jamozu/multisensor/pics/Pic_AQS_Base02.jpg

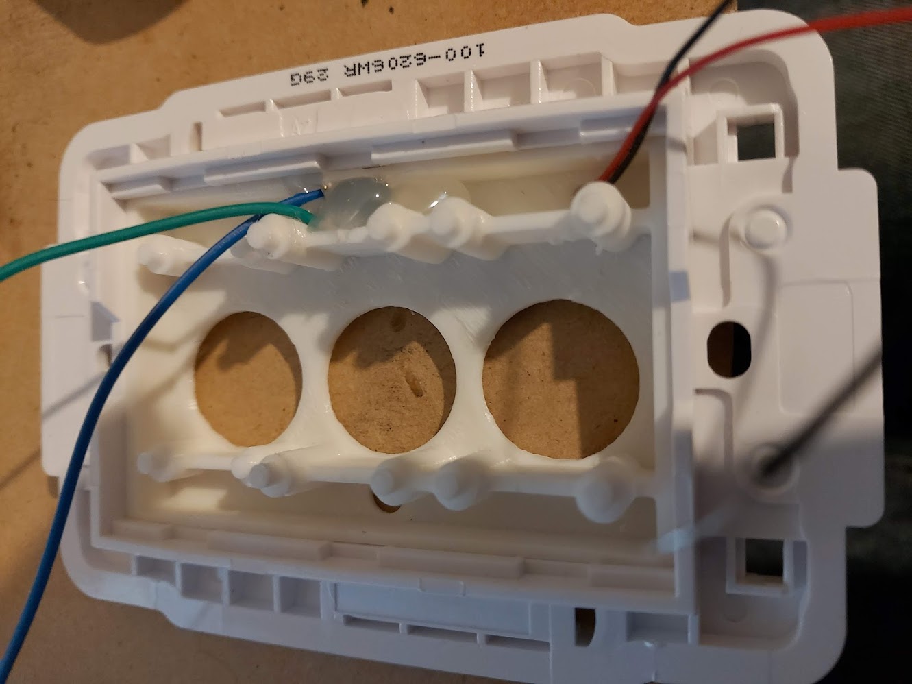
pics/Pic_AQS_Base02.jpg
