jamozu/multisensor/pics/Pic_AQS_faceplate.jpg

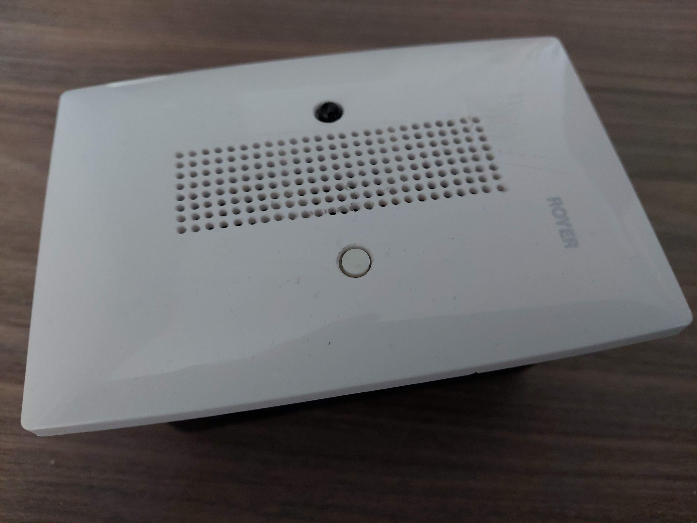
pics/Pic_AQS_faceplate.jpg
