jamozu/multisensor/pics/Pic_AQS_PCB.jpg

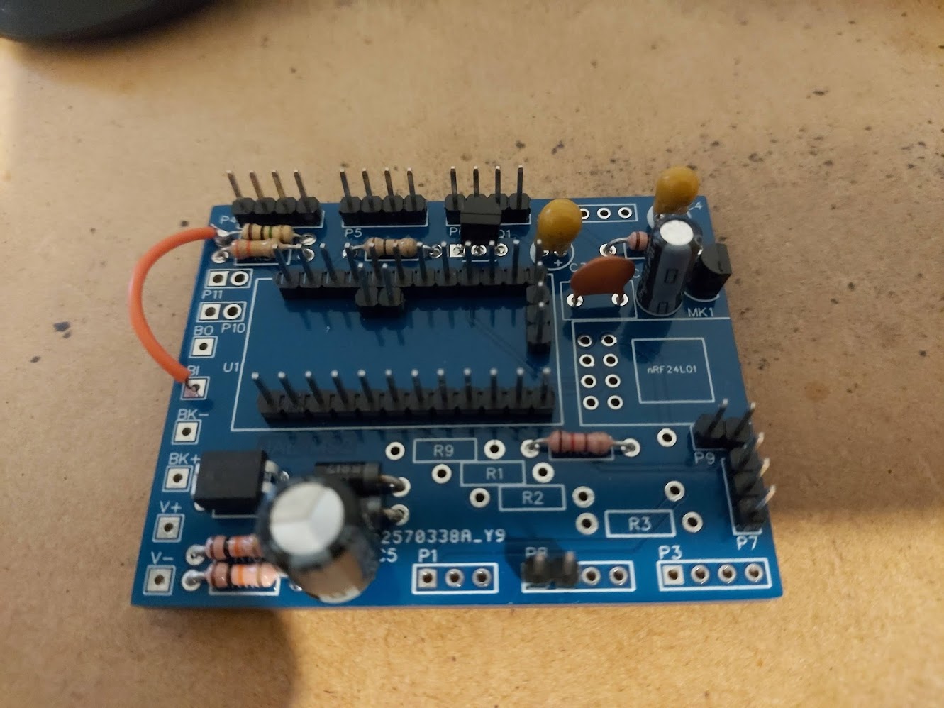
pics/Pic_AQS_PCB.jpg
