jamozu/multisensor/pics/Pic_Module_Power01.jpg

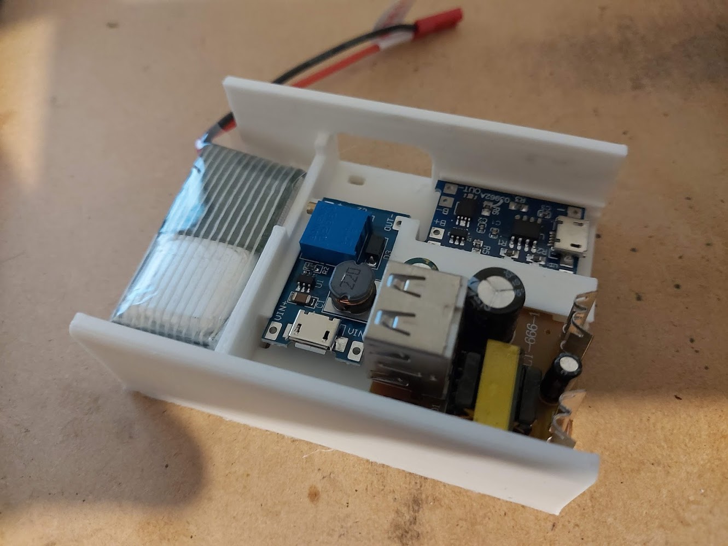
pics/Pic_Module_Power01.jpg
