jamozu/multisensor/pics/Pic_Module_Power02.jpg

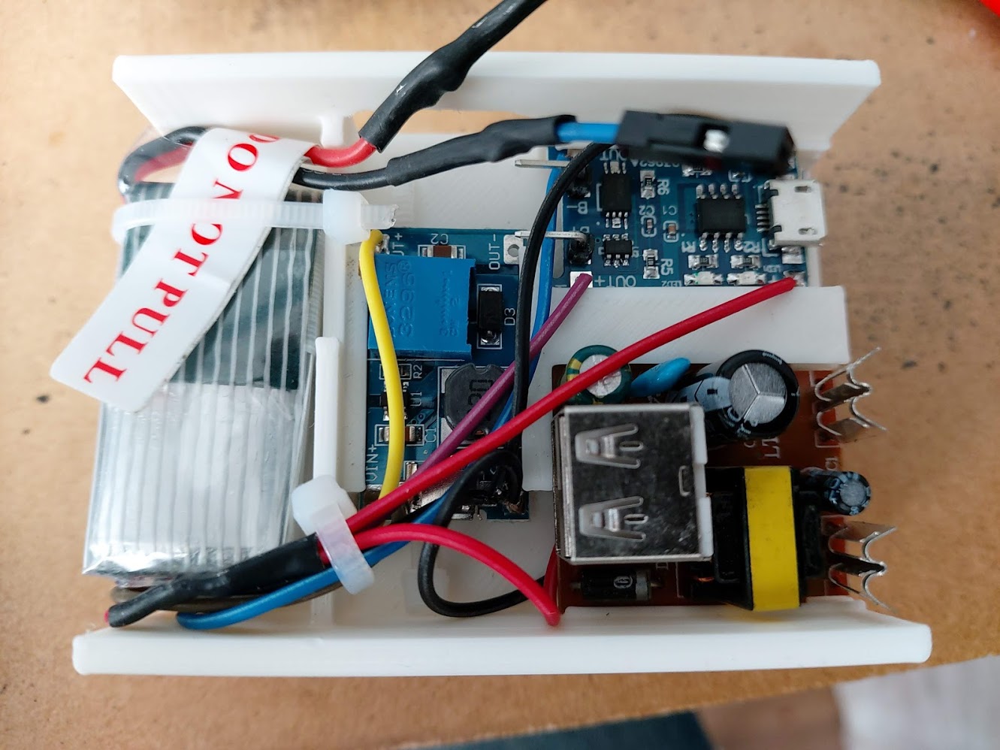
pics/Pic_Module_Power02.jpg
