jamozu/multisensor/pics/Pic_Module_Power_BatBackup.jpg

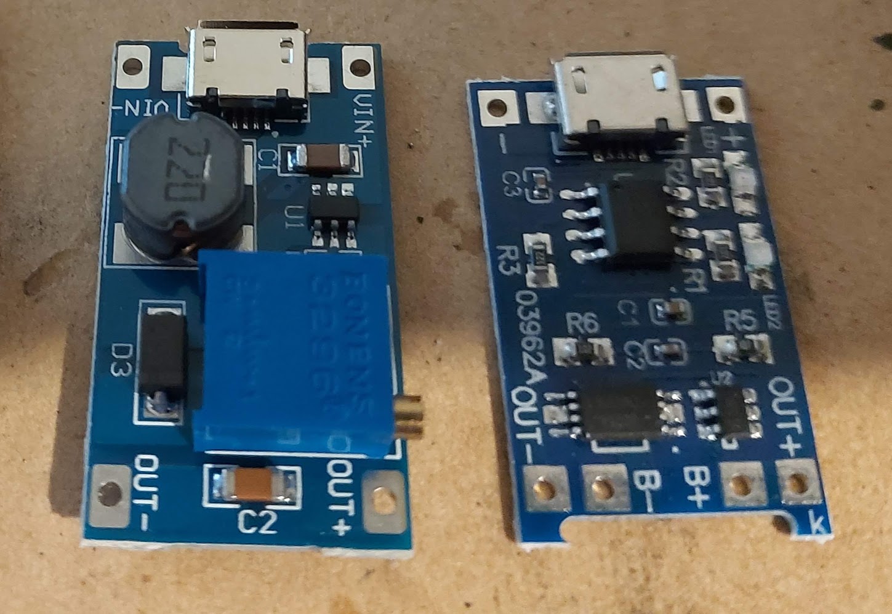
pics/Pic_Module_Power_BatBackup.jpg
