jamozu/multisensor/pics/Pic_Motion_Base.jpg

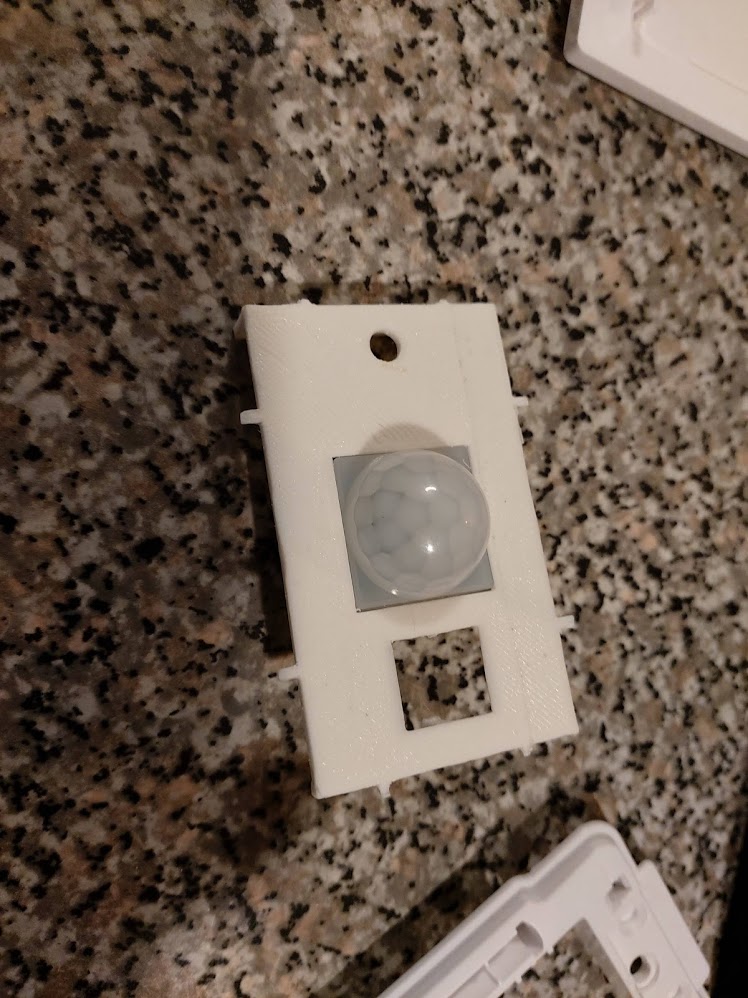
pics/Pic_Motion_Base.jpg
