jamozu/multisensor/pics/Pic_Motion_Sensors.jpg

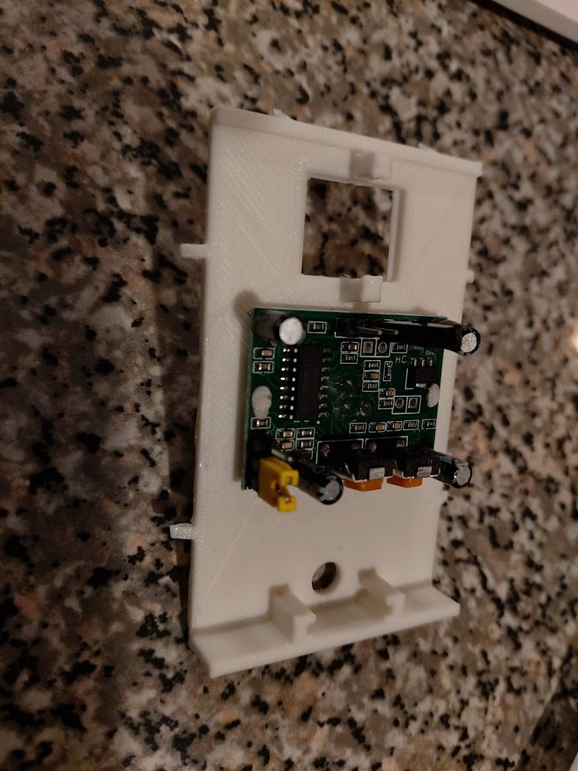
pics/Pic_Motion_Sensors.jpg
