jamozu/multisensor/pics/Pic_PCB.jpg

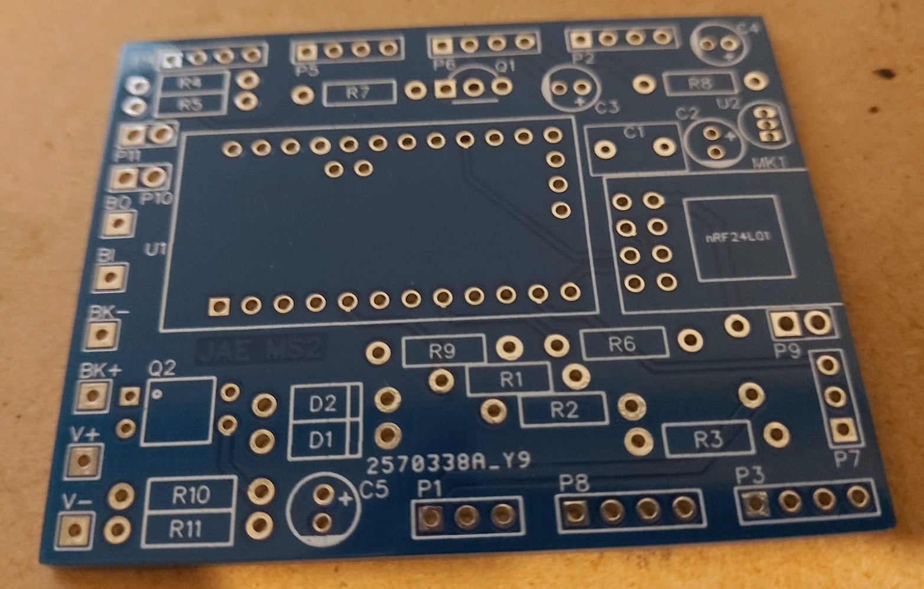
pics/Pic_PCB.jpg
